gcapora/ISPEL-CAD/Info/Hojas de datos/Transistores/2SD882_NEC.pdf

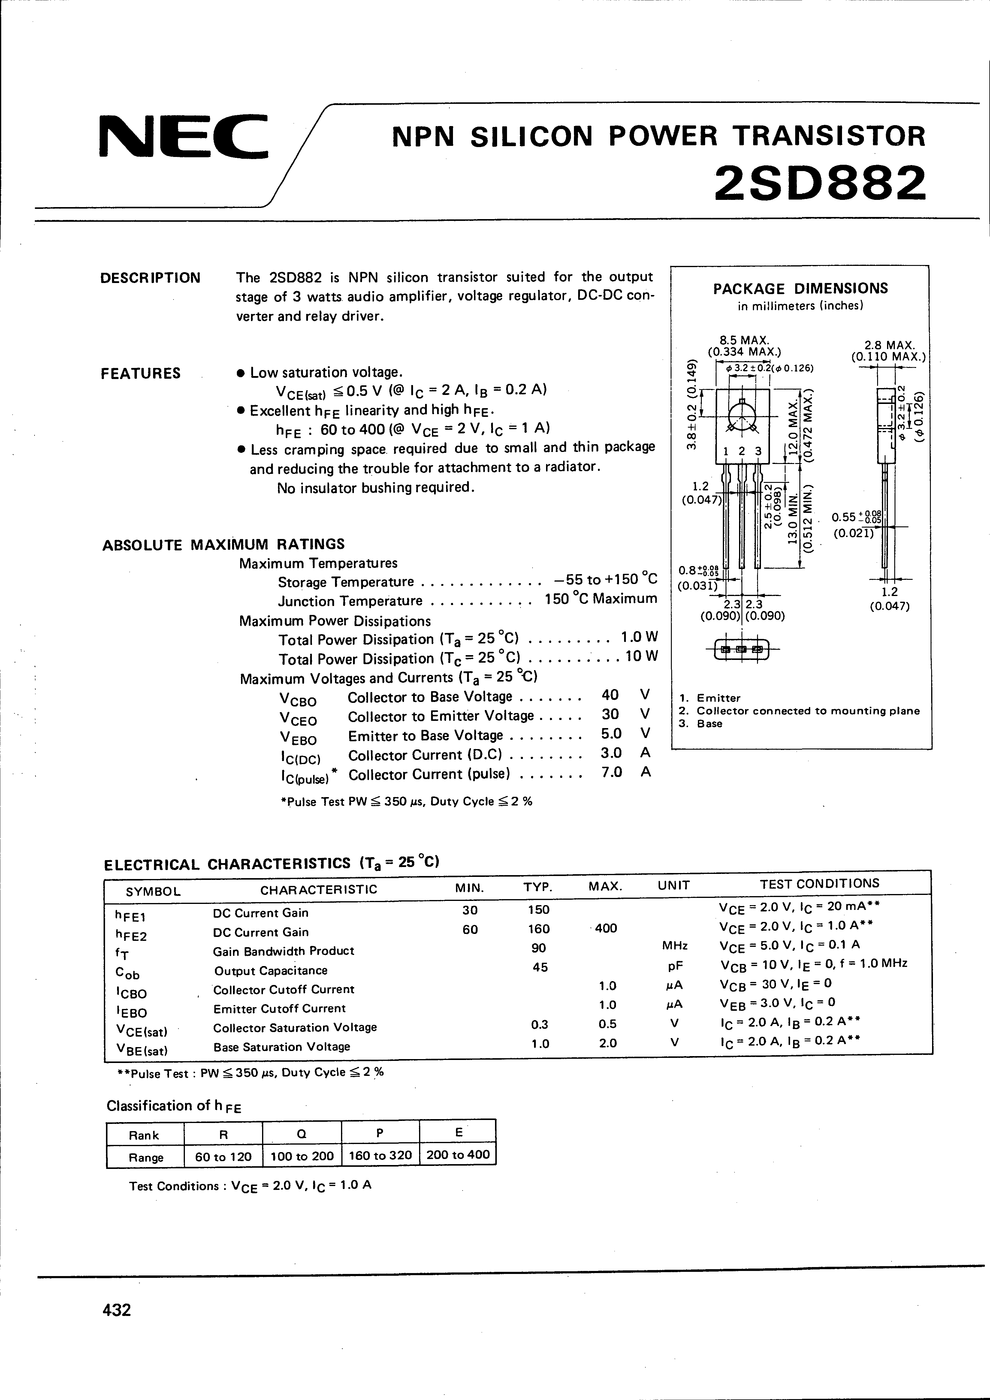
[picture p2: page 1]
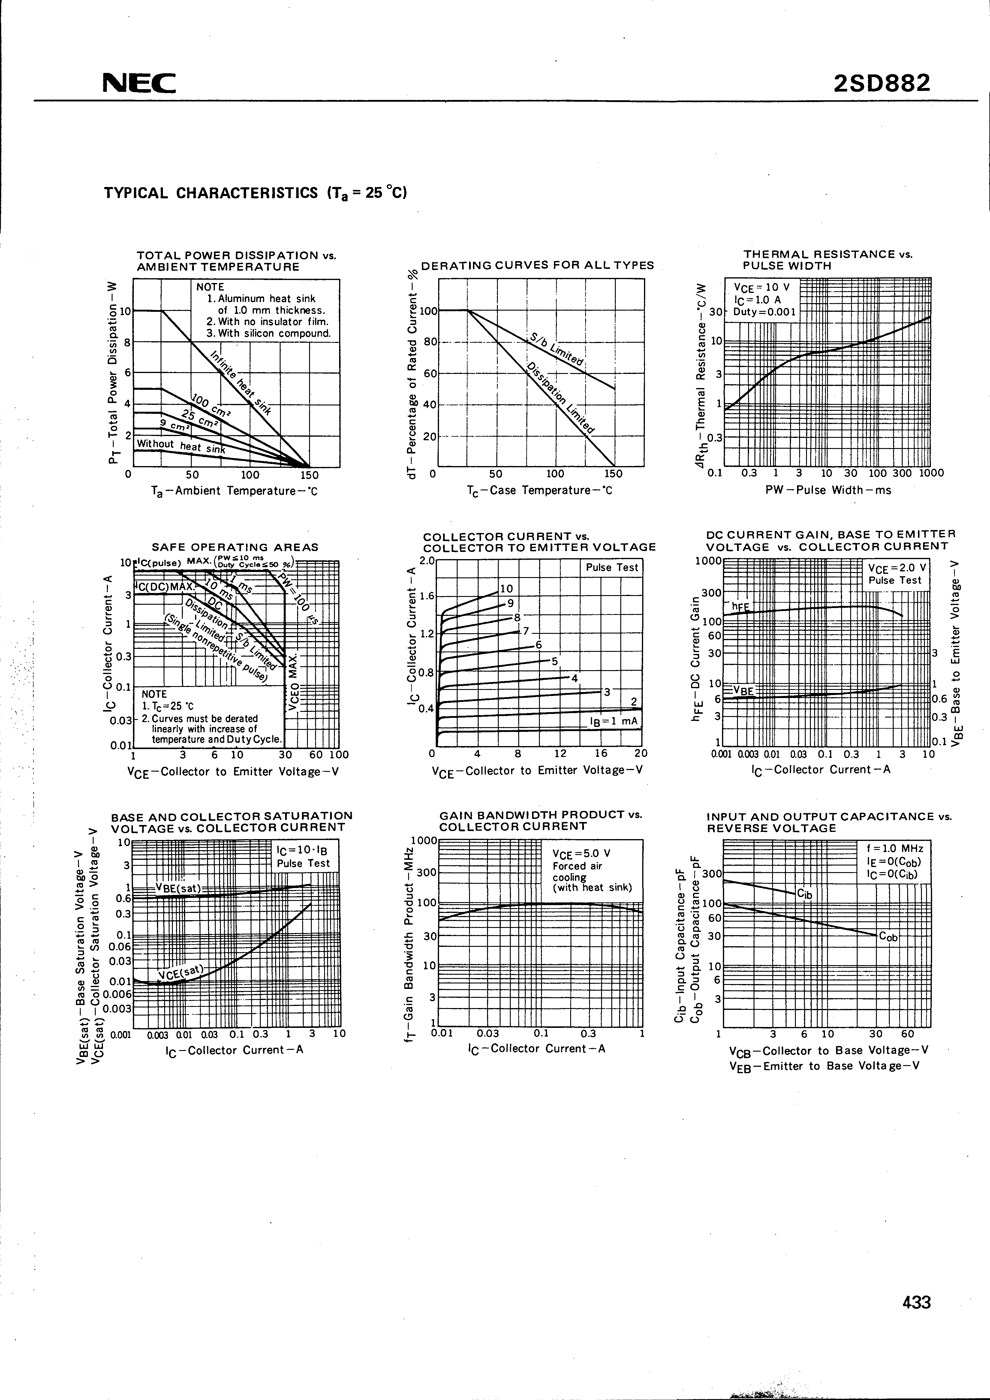
[picture p3: page 2]
